cidte/EstacionTerrena/Electrónica/PCB/magnetometro/pcb2_PCB1_855037550_etch_copper_bottom.pdf

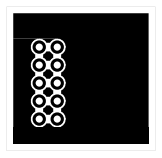
[picture p6: figure]
