cidte/EstacionTerrena/Electrónica/PCB/magnetometro/pcb2_PCB1_855037550_etch_copper_bottom_mirror.pdf

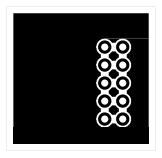
[picture p7: figure]
