cidte/EstacionTerrena/Electrónica/PCB/magnetometro/pcb2_PCB1_855037550_etch_copper_top.pdf

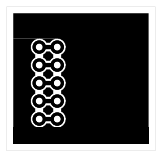
[picture p8: figure]
