cidte/EstacionTerrena/Electrónica/PCB/magnetometro/pcb2_PCB1_855037550_etch_copper_top_mirror.pdf

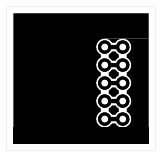
[picture p9: figure]
