cidte/EstacionTerrena/Electrónica/PCB/magnetometro/pcb2_PCB1_855037550_etch_mask_bottom.pdf

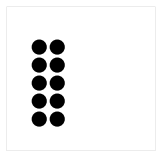
[picture p10: figure]
