cidte/EstacionTerrena/Electrónica/PCB/magnetometro/pcb2_PCB1_855037550_etch_mask_bottom_mirror.pdf

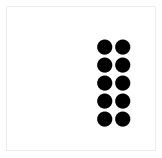
[picture p11: figure]
