cidte/EstacionTerrena/Electrónica/PCB/elevacion/pcb2_PCB1_855035920_etch_mask_bottom.pdf

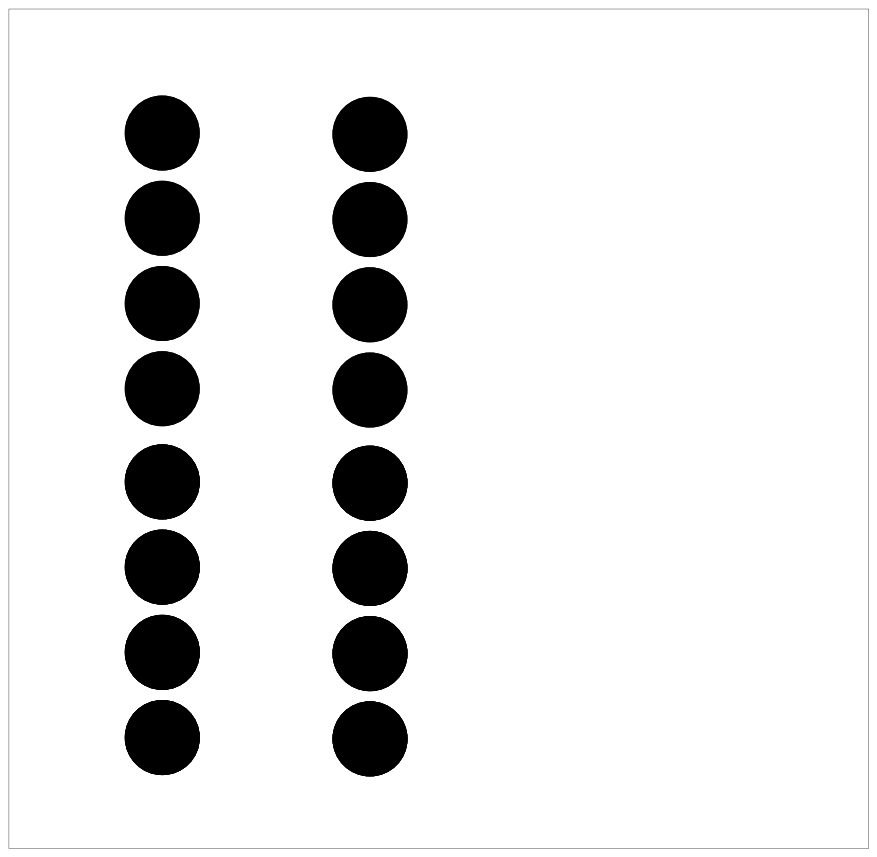
[picture p26: page 1]
