cidte/EstacionTerrena/Electrónica/PCB/elevacion/pcb2_PCB1_855035920_etch_mask_bottom_mirror.pdf

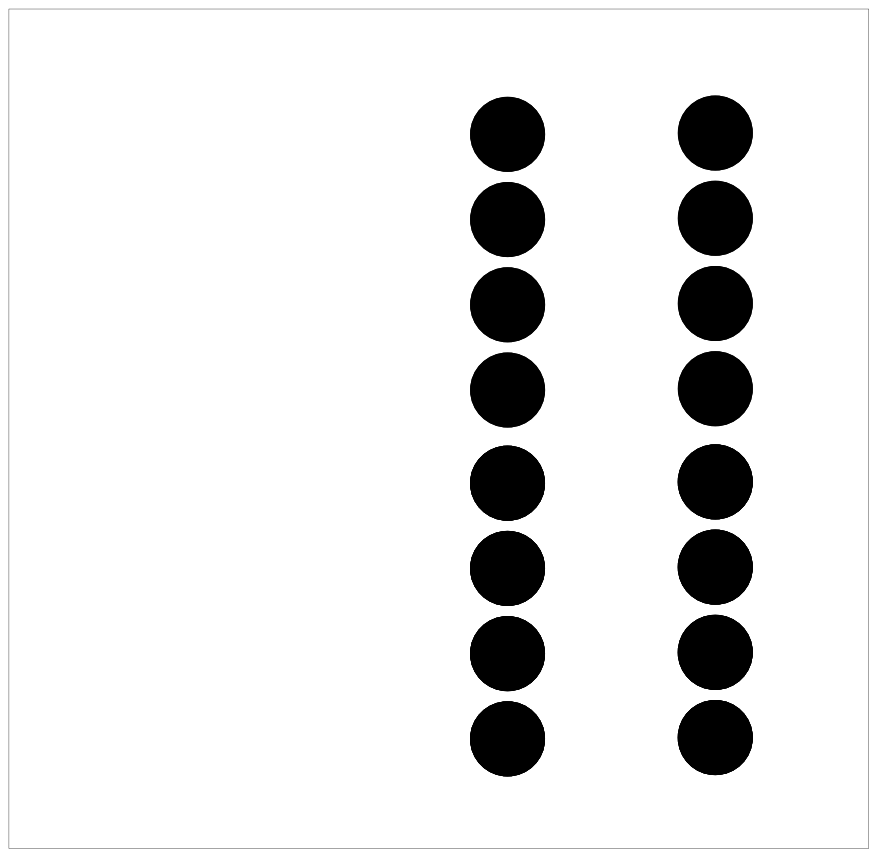
[picture p27: page 1]
