cidte/EstacionTerrena/Electrónica/PCB/magnetometro/pcb2_PCB1_855037550_etch_mask_top.pdf

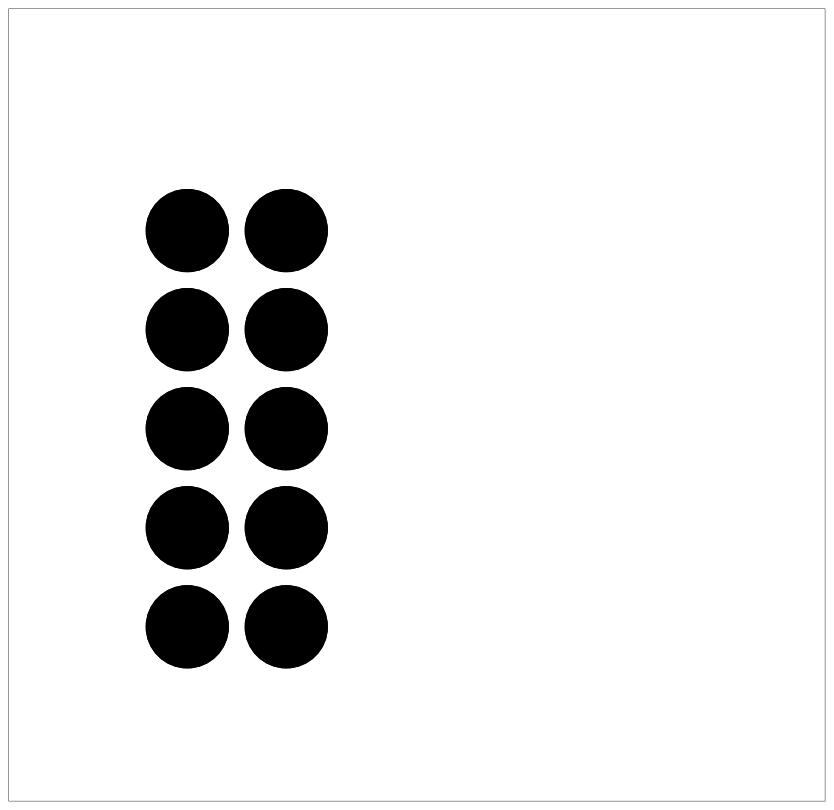
[picture p28: page 1]
