cidte/EstacionTerrena/Electrónica/PCB/magnetometro/pcb2_PCB1_855037550_etch_mask_top_mirror.pdf

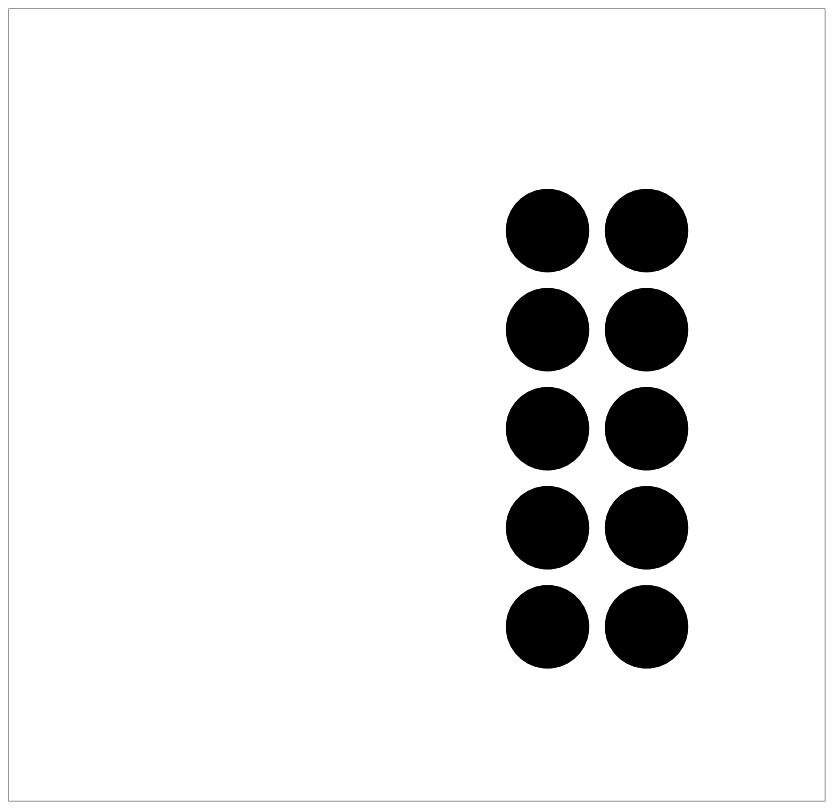
[picture p29: page 1]
